karltamm/easyPlay/hardware/Outputs/PCB 3D Print/PCB 3D model bottom.png

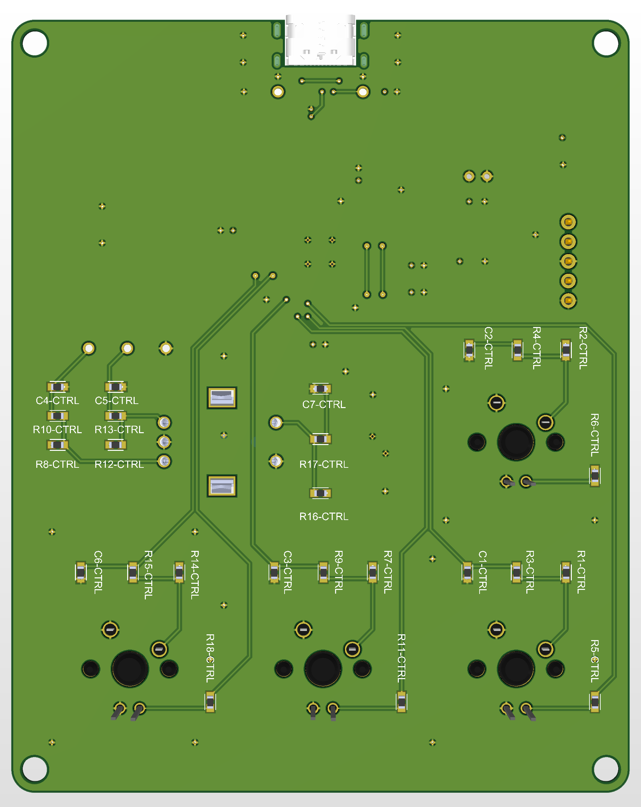
hardware/Outputs/PCB 3D Print/PCB 3D model bottom.png
