karltamm/easyPlay/hardware/Outputs/PCB 3D Print/PCB 3D model top.png

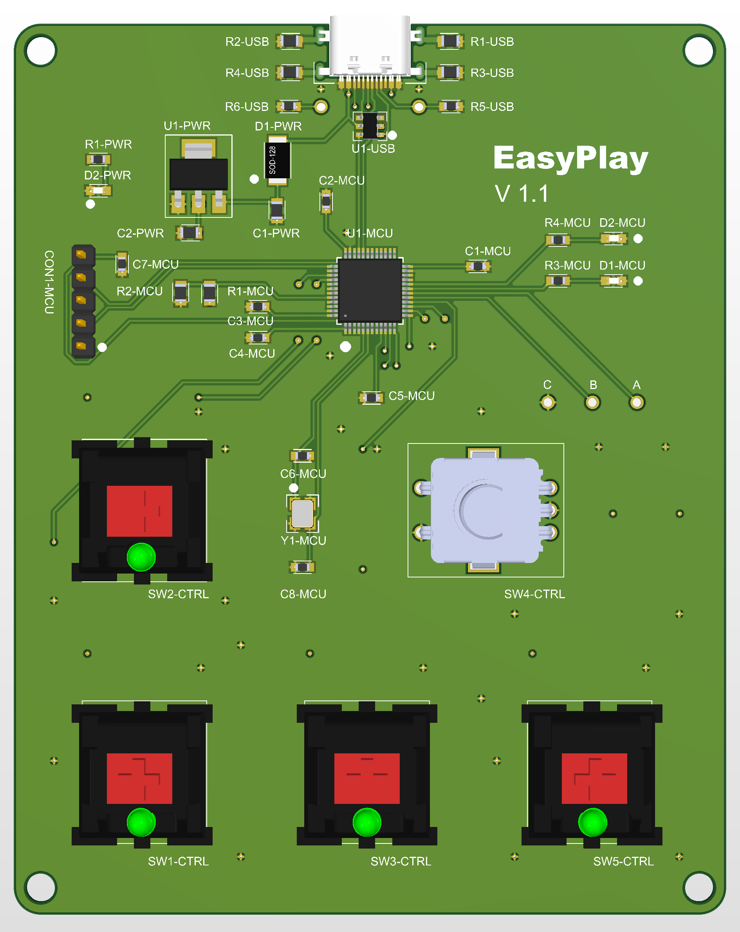
hardware/Outputs/PCB 3D Print/PCB 3D model top.png
